SsimonSA/church-drain-monitor/firmware/photos/22-enclosure-inside-buzzer-side.jpg

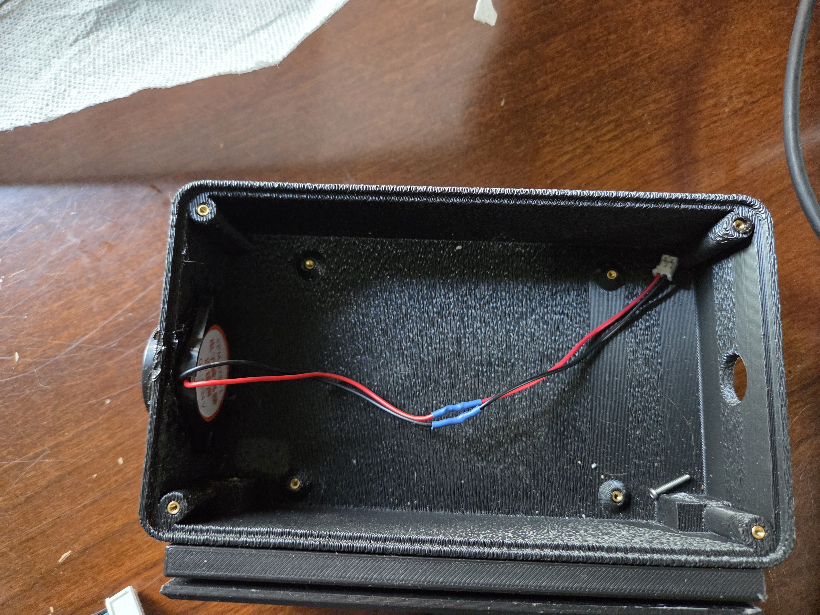
firmware/photos/22-enclosure-inside-buzzer-side.jpg
