SsimonSA/church-drain-monitor/firmware/photos/23-enclosure-angled-with-mount.jpg

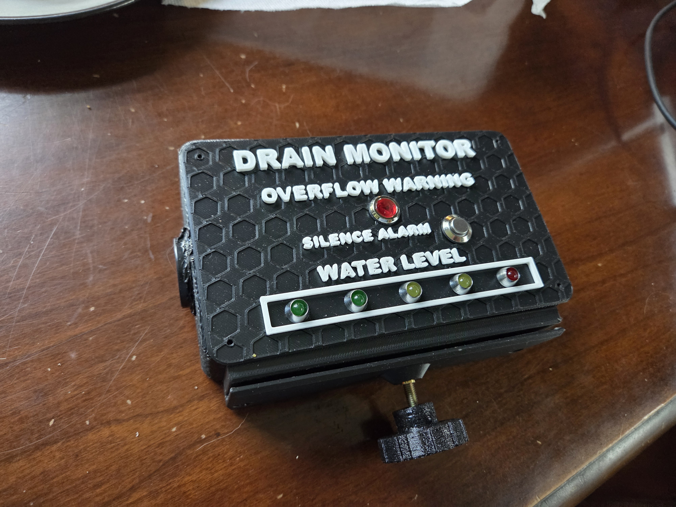
firmware/photos/23-enclosure-angled-with-mount.jpg
