SsimonSA/church-drain-monitor/firmware/photos/24-sr04-cap-detached.jpg

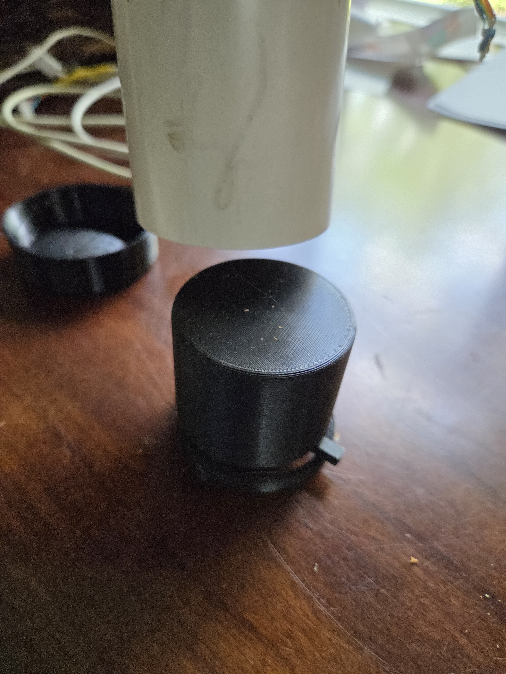
firmware/photos/24-sr04-cap-detached.jpg
